TobiasJaeggi/fpga-mocap/visionAddOn/pcb/3DModels/RT2012-32.768-9-20-EXT-TR.stp

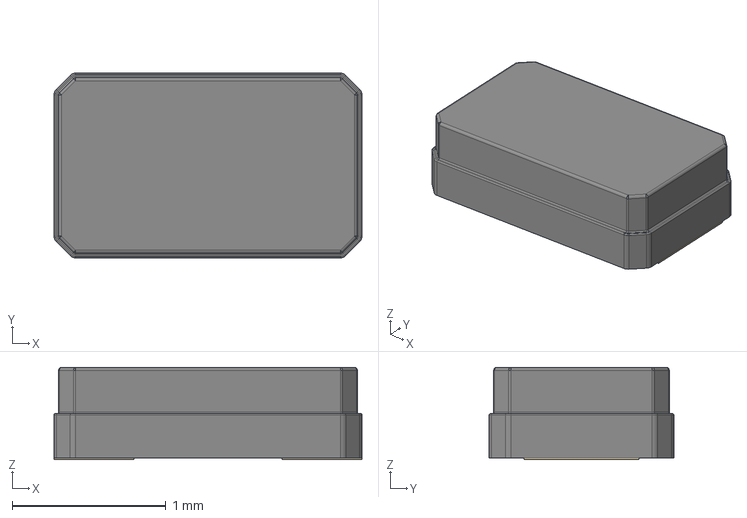
[picture p15: CAD file, 2025-07-20]
visionAddOn/pcb/3DModels/RT2012-32.768-9-20-EXT-TR.stp
2.00 x 1.20 x 0.6 mm
