TobiasJaeggi/fpga-mocap/visionAddOn/pcb/3DModels/Amass_XT30UPB-F.step

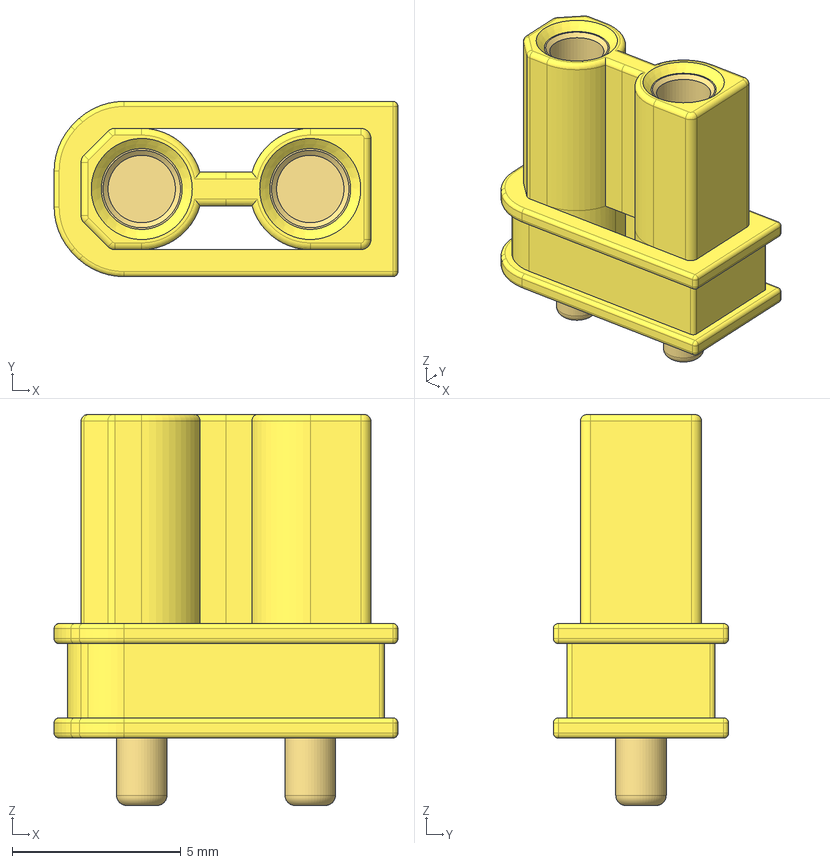
[picture p16: CAD file, 2025-07-20]
visionAddOn/pcb/3DModels/Amass_XT30UPB-F.step
10.2 x 5.20 x 11.6 mm
