TobiasJaeggi/fpga-mocap/visionAddOn/pcb/3DModels/USB2513B-AEZC-TR.STEP

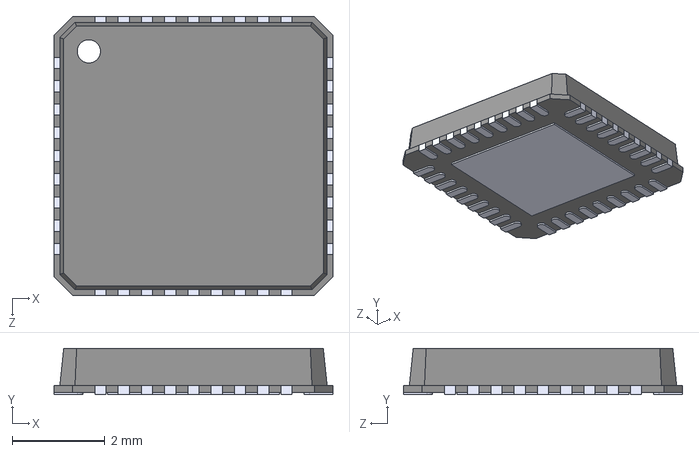
[picture p17: CAD file, 2025-07-20]
visionAddOn/pcb/3DModels/USB2513B-AEZC-TR.STEP
6.00 x 1.00 x 6.00 mm
