TobiasJaeggi/fpga-mocap/visionAddOn/pcb/3DModels/ARJP11A-MASA-B-A-EMU2--3DModel-STEP-1.STEP

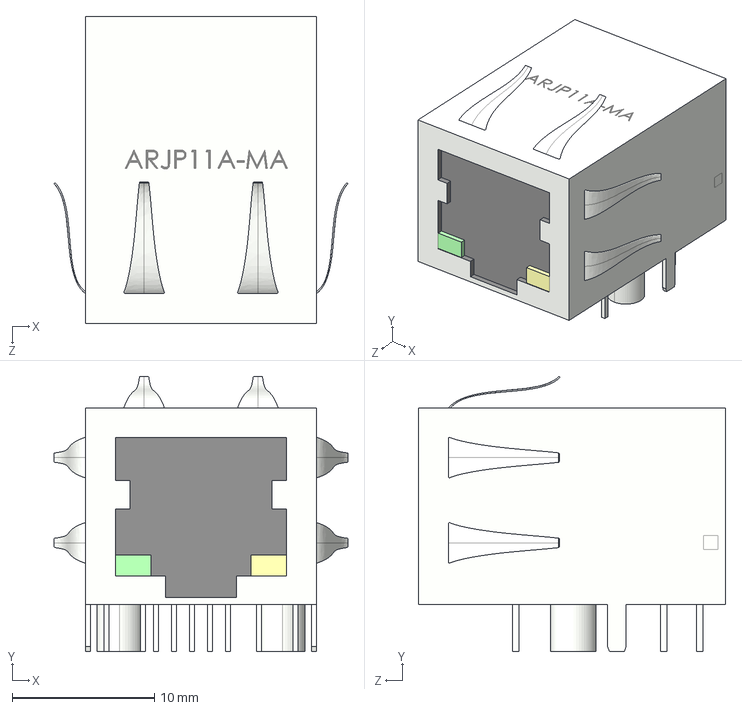
[picture p18: CAD file, 2025-07-20]
visionAddOn/pcb/3DModels/ARJP11A-MASA-B-A-EMU2--3DModel-STEP-1.STEP
20.7 x 19.3 x 21.6 mm
