TobiasJaeggi/fpga-mocap/visionAddOn/pcb/3DModels/LAN8742A-CZ-TR--3DModel-STEP-510211.STEP

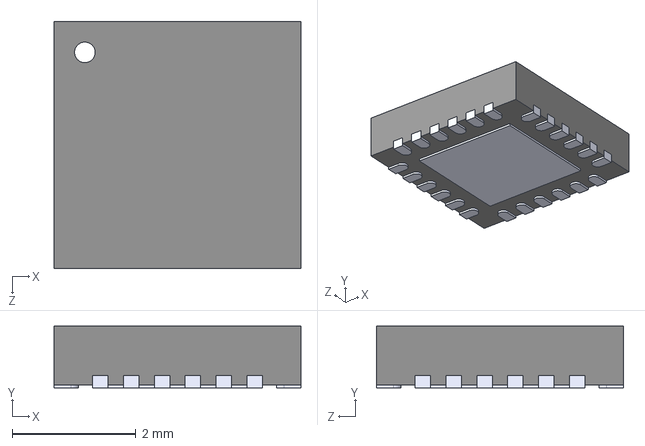
[picture p19: CAD file, 2025-07-20]
visionAddOn/pcb/3DModels/LAN8742A-CZ-TR--3DModel-STEP-510211.STEP
4.00 x 1.00 x 4.00 mm
