TobiasJaeggi/fpga-mocap/visionAddOn/pcb/3DModels/NTS0104BQ_115.step

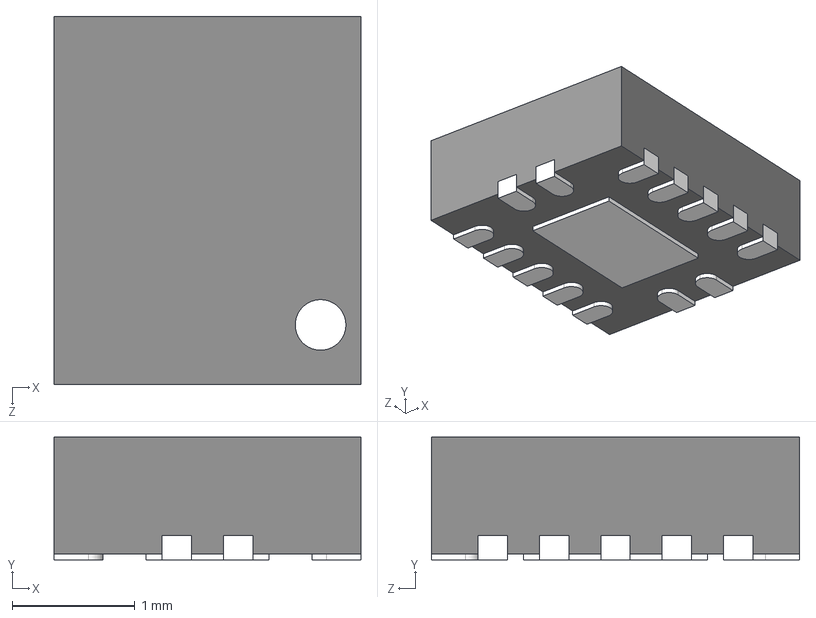
[picture p20: CAD file, 2025-07-20]
visionAddOn/pcb/3DModels/NTS0104BQ_115.step
2.50 x 1.00 x 3.00 mm
