TobiasJaeggi/fpga-mocap/visionAddOn/pcb/3DModels/MYBSP0055AABFT--3DModel-STEP-387902.STEP

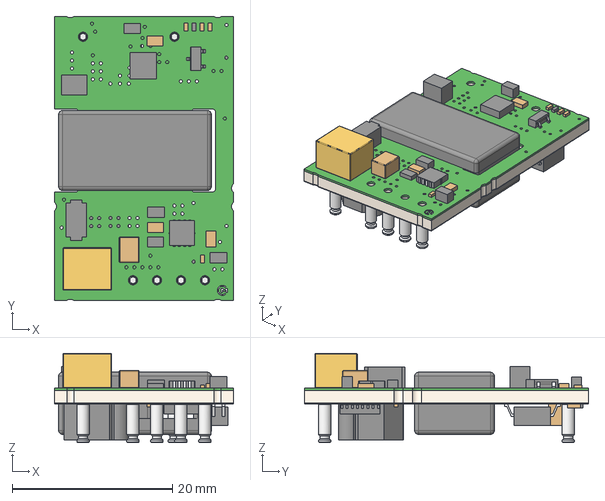
[picture p21: CAD file, 2025-07-20]
visionAddOn/pcb/3DModels/MYBSP0055AABFT--3DModel-STEP-387902.STEP
22.4 x 35.5 x 11.1 mm
