TobiasJaeggi/fpga-mocap/visionAddOn/pcb/3DModels/QTE-020-01-X-D-A.step

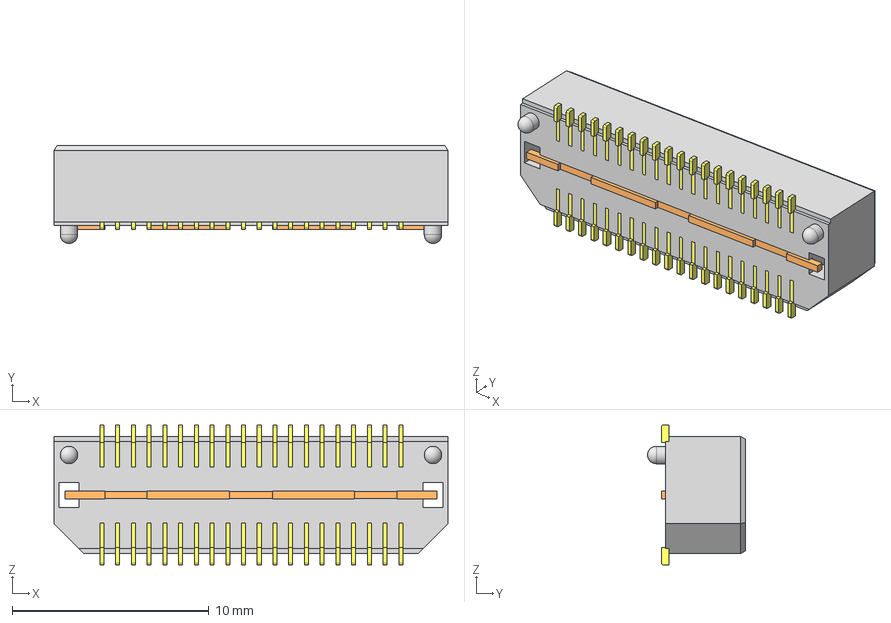
[picture p22: CAD file, 2025-07-20]
visionAddOn/pcb/3DModels/QTE-020-01-X-D-A.step
20.0 x 4.98 x 7.11 mm
QTE-T-1G1-01_imp
PT-1S39-01(020-01-D)
QTE-020-01-D-At
