TobiasJaeggi/fpga-mocap/visionAddOn/pcb/3DModels/LQM2HPN2R2MJ0L.STEP

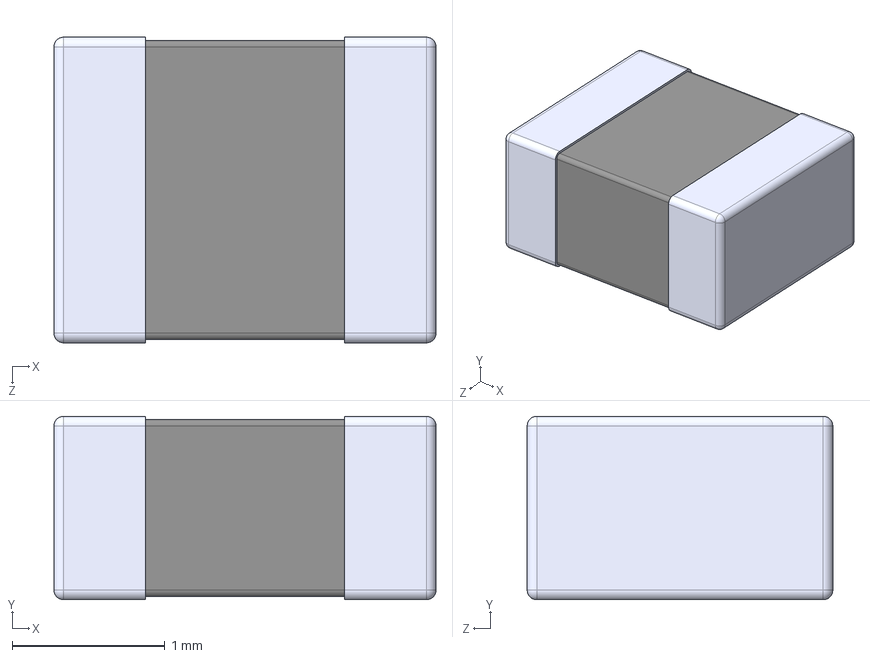
[picture p23: CAD file, 2025-07-20]
visionAddOn/pcb/3DModels/LQM2HPN2R2MJ0L.STEP
2.50 x 1.20 x 2.00 mm
