TobiasJaeggi/fpga-mocap/visionAddOn/firmware/Core/Src/main.cpp

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
/* Includes ------------------------------------------------------------------*/
#include "main.h"
#include "cmsis_os.h"
#include "dcmi.h"
#include "dma.h"
#include "i2c.h"
#include "lwip.h"
#include "spi.h"
#include "usart.h"
#include "usb_otg.h"
#include "gpio.h"
#include "fmc.h"

/* USER CODE BEGIN Includes */

#include <stdio.h>
/* USER CODE END Includes */

/* USER CODE BEGIN PD */
#define TEST_EXTERNAL_SDRAM
#define LWIP_DEBUG 1
#undef SOCKETS_DEBUG
#define SOCKETS_DEBUG LWIP_DBG_ON
#undef MEM_DEBUG
#define MEM_DEBUG LWIP_DBG_ON
#undef MEMP_DEBUG
#define MEMP_DEBUG LWIP_DBG_ON
/* USER CODE END PD */


void SystemClock_Config(void);
void MX_FREERTOS_Init(void);
/* USER CODE BEGIN 0 */
}
#include "AppBuilder.h"
#include "utils/swo.h"
#include "utils/Log.h"
#include "utils/constants.h"
#include "as4c16m16msa/sdram.h"
/* USER CODE END 0 */

/**
  * @brief  The application entry point.
  * @retval int
  */
int main(void)
{

  /* MCU Configuration--------------------------------------------------------*/

  /* Reset of all peripherals, Initializes the Flash interface and the Systick. */
  HAL_Init();

  /* Configure the system clock */
  SystemClock_Config();

  /* Initialize all configured peripherals */
  MX_GPIO_Init();
  MX_DMA_Init();
  MX_DCMI_Init();
  MX_FMC_Init();
  MX_USART1_UART_Init();
  MX_USART2_UART_Init();
  MX_I2C1_Init();
  MX_SPI1_Init();
  MX_I2C4_Init();
  MX_SPI5_Init();
  MX_UART5_Init();
  MX_USB_OTG_HS_PCD_Init();
  /* USER CODE BEGIN 2 */
  Log::registerTickKeeper([](void) -> uint32_t {return osKernelGetTickCount();});
  Log::setTickrate(TICKS_PER_MILLISECOND);
  Log::level(Log::Level::LOG_INFO);
  Log::info("[main] visionAddOn, commit %s", GIT_COMMIT_HASH);

  initSdram(&hsdram1);
#ifdef TEST_EXTERNAL_SDRAM
  Log::info("[main] testing sdram");
  uint32_t* externalSdramBase = (uint32_t*) EXTERNAL_SDRAM_BASE_ADDRESS;
  for(uint32_t offset = 0; offset < EXTERNAL_SDRAM_SIZE_WORDS; offset++) {
    if((EXTERNAL_SDRAM_BASE_ADDRESS + offset) > EXTERNAL_SDRAM_END_ADDRESS) {
      Log::error("[main] @ offset %#x: EXTERNAL_SDRAM_BASE_ADDRESS + offset = %#x, which is greater than EXTERNAL_SDRAM_END_ADDRESS (%#x)", offset, EXTERNAL_SDRAM_BASE_ADDRESS + offset, EXTERNAL_SDRAM_END_ADDRESS);
      Error_Handler();
    }
    externalSdramBase[offset] = offset;
    uint32_t offsetReadBack = externalSdramBase[offset];
    if(offset != offsetReadBack) {
      Log::error("[main] offset: %#x, offsetReadBack: %#x", offset, offsetReadBack);
      Error_Handler();
    }
  }
  Log::info("[main] sdram ok");
#endif // TEST_EXTERNAL_SDRAM

  /* USER CODE END 2 */

  /* Init scheduler */
  osKernelInitialize();

  /* Call init function for freertos objects (in cmsis_os2.c) */
  MX_FREERTOS_Init();

  /* Start scheduler */
  osKernelStart();

  /* We should never get here as control is now taken by the scheduler */

  /* Infinite loop */
  /* USER CODE BEGIN WHILE */

  
  while (1)
  {
    /* USER CODE END WHILE */

    /* USER CODE BEGIN 3 */
  } // extern C
// ignore the shitty RCC_OscInitStruct and RCC_ClkInitStruct initialization
#pragma GCC diagnostic push
#pragma GCC diagnostic ignored "-Wmissing-field-initializers"
  /* USER CODE END 3 */
}

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
/* USER CODE BEGIN 4 */
#pragma GCC diagnostic pop // "-Wmissing-field-initializers"
/* USER CODE END 4 */

/**
  * @brief  Period elapsed callback in non blocking mode
  * @note   This function is called  when TIM1 interrupt took place, inside
  * HAL_TIM_IRQHandler(). It makes a direct call to HAL_IncTick() to increment
  * a global variable "uwTick" used as application time base.
  * @param  htim : TIM handle
  * @retval None
  */
void HAL_TIM_PeriodElapsedCallback(TIM_HandleTypeDef *htim)
{
  if (htim->Instance == TIM1) {
    HAL_IncTick();
  }
}

/**
  * @brief  This function is executed in case of error occurrence.
  * @retval None
  */
void Error_Handler(void)
{
  /* USER CODE BEGIN Error_Handler_Debug */
  /* User can add his own implementation to report the HAL error return state */
  __disable_irq();
  log_error("[Error_Handler]");
  abort();
  /* USER CODE END Error_Handler_Debug */
}

#ifdef  USE_FULL_ASSERT
/**
  * @brief  Reports the name of the source file and the source line number
  *         where the assert_param error has occurred.
  * @param  file: pointer to the source file name
  * @param  line: assert_param error line source number
  * @retval None
  */
void assert_failed(uint8_t *file, uint32_t line)
{
  /* USER CODE BEGIN 6 */
  /* User can add his own implementation to report the file name and line number,
     ex: printf("Wrong parameters value: file %s on line %d\r\n", file, line) */
  /* USER CODE END 6 */
}
#endif /* USE_FULL_ASSERT */
