TobiasJaeggi/fpga-mocap/visionAddOn/pcb/STM32F767ZIx/STM32F767ZIx.ioc

Mcu.UserName=STM32F767ZITx
PA0/WKUP.GPIO_Label=STM_DBG_10
PA0/WKUP.Signal=GPIO_Input
PA1.Signal=ETH_REF_CLK
PA10.Signal=USART1_RX
PA11.Signal=USART1_CTS
PA12.Signal=USART1_RTS
PA13.GPIO_Label=TMS
PA13.Signal=SYS_JTMS-SWDIO
PA14.GPIO_Label=TCK
PA14.Signal=SYS_JTCK-SWCLK
PA15.Signal=SYS_JTDI
PA2.Signal=ETH_MDIO
PA3.Signal=USART2_RX
PA4.Signal=DCMI_HSYNC
PA5.Signal=SPI1_SCK
PA6.Signal=DCMI_PIXCLK
PA7.Signal=ETH_CRS_DV
PA8.GPIO_Label=STM_DBG_11
PA8.Signal=GPIO_Input
PA9.Signal=USART1_TX
PB0.GPIO_Label=STM_DBG_15
PB0.Signal=GPIO_Input
PB1.GPIO_Label=STM_DBG_16
PB1.Signal=GPIO_Input
PB10.GPIO_Label=STM_DBG_21
PB10.Signal=GPIO_Input
PB11.Signal=ETH_TX_EN
PB12.Signal=ETH_TXD0
PB13.Signal=ETH_TXD1
PB14.Signal=USB_OTG_HS_DM
PB15.Signal=USB_OTG_HS_DP
PB2.GPIO_Label=STM_DBG_17
PB2.Signal=GPIO_Input
PB3.GPIO_Label=SWO
PB3.Signal=SYS_JTDO-SWO
PB4.Signal=SPI1_MISO
PB5.GPIO_Label=STM_DBG_18
PB5.Signal=GPIO_Input
PB6.Signal=I2C1_SCL
PB7.Signal=I2C1_SDA
PB8.Signal=UART5_RX
PB9.Signal=UART5_TX
PC0.Signal=FMC_SDNWE
PC1.Signal=ETH_MDC
PC10.GPIO_Label=STM_DBG_23
PC10.Signal=GPIO_Input
PC11.GPIO_Label=STM_DBG_24
PC11.Signal=GPIO_Input
PC12.GPIO_Label=STM_DBG_20
PC12.Signal=GPIO_Input
PC13.GPIO_Label=BUTTON1
PC13.Signal=GPIO_Input
PC14/OSC32_IN.Signal=RCC_OSC32_IN
PC15/OSC32_OUT.Signal=RCC_OSC32_OUT
PC2.Signal=FMC_SDNE0
PC3.Signal=FMC_SDCKE0
PC4.Signal=ETH_RXD0
PC5.Signal=ETH_RXD1
PC6.Signal=DCMI_D0
PC7.Signal=DCMI_D1
PC8.Signal=DCMI_D2
PC9.Signal=DCMI_D3
PD0.Signal=FMC_D2_DA2
PD1.Signal=FMC_D3_DA3
PD10.Signal=FMC_D15_DA15
PD11.GPIO_Label=WATCHDOG
PD11.Signal=GPIO_Output
PD12.Signal=I2C4_SCL
PD13.Signal=I2C4_SDA
PD14.Signal=FMC_D0_DA0
PD15.Signal=FMC_D1_DA1
PD2.GPIO_Label=STM_DBG_19
PD2.Signal=GPIO_Input
PD3.Signal=DCMI_D5
PD4.GPIO_Label=STM_DBG_8
PD4.Signal=GPIO_Input
PD5.Signal=USART2_TX
PD6.GPIO_Label=STM_DGB_25
PD6.Signal=GPIO_Input
PD7.Signal=SPI1_MOSI
PD8.Signal=FMC_D13_DA13
PD9.Signal=FMC_D14_DA14
PE0.Signal=FMC_NBL0
PE1.Signal=FMC_NBL1
PE10.Signal=FMC_D7_DA7
PE11.Signal=FMC_D8_DA8
PE12.Signal=FMC_D9_DA9
PE13.Signal=FMC_D10_DA10
PE14.Signal=FMC_D11_DA11
PE15.Signal=FMC_D12_DA12
PE2.GPIO_Label=LED_RED
PE2.Signal=GPIO_Output
PE3.GPIO_Label=LED_GREEN
PE3.Signal=GPIO_Output
PE4.Signal=DCMI_D4
PE5.Signal=DCMI_D6
PE6.Signal=DCMI_D7
PE7.Signal=FMC_D4_DA4
PE8.Signal=FMC_D5_DA5
PE9.Signal=FMC_D6_DA6
PF0.Signal=FMC_A0
PF1.Signal=FMC_A1
PF10.GPIO_Label=STM_DBG_9
PF10.Signal=GPIO_Input
PF11.Signal=FMC_SDNRAS
PF12.Signal=FMC_A6
PF13.Signal=FMC_A7
PF14.Signal=FMC_A8
PF15.Signal=FMC_A9
PF2.Signal=FMC_A2
PF3.Signal=FMC_A3
PF4.Signal=FMC_A4
PF5.Signal=FMC_A5
PF6.GPIO_Label=POE_TYPE
PF6.Signal=GPIO_Input
PF7.Signal=SPI5_SCK
PF8.Signal=SPI5_MISO
PF9.Signal=SPI5_MOSI
PG0.Signal=FMC_A10
PG1.Signal=FMC_A11
PG10.GPIO_Label=STM_DBG_3
PG10.Signal=GPIO_Input
PG11.GPIO_Label=STM_DBG_4
PG11.Signal=GPIO_Input
PG12.GPIO_Label=STM_DBG_5
PG12.Signal=GPIO_Input
PG13.GPIO_Label=STM_DBG_6
PG13.Signal=GPIO_Input
PG14.GPIO_Label=STM_DBG_7
PG14.Signal=GPIO_Input
PG15.Signal=FMC_SDNCAS
PG2.Signal=FMC_A12
PG3.GPIO_Label=STM_DBG_0
PG3.Signal=GPIO_Input
PG4.Signal=FMC_A14_BA0
PG5.Signal=FMC_A15_BA1
PG6.GPIO_Label=STM_DBG_1
PG6.Signal=GPIO_Input
PG7.GPIO_Label=STM_DBG_2
PG7.Signal=GPIO_Input
PG8.Signal=FMC_SDCLK
PG9.Signal=DCMI_VSYNC
PH0/OSC_IN.Signal=RCC_OSC_IN
PH1/OSC_OUT.Signal=RCC_OSC_OUT
