TobiasJaeggi/fpga-mocap/gecko5/hdl/modules/counters/verilog/intCounter.v

module intCounter #(parameter MAX = 20) (
  input wire clock,
  input wire reset,
  input wire clear,
  input wire load,
  input wire enable,
  input wire [$clog2(MAX)-1:0] din,
  output wire max_pulse,
  output wire [$clog2(MAX)-1:0] dout
);

reg[$clog2(MAX)-1:0] s_stateNext, s_stateReg;

//TODO: async reset
always @(posedge clock)
begin
  s_stateReg <= ((reset == 1'b1) || (s_stateNext == $clog2(MAX)'(MAX))) ? 0 : s_stateNext;
end

// NSL
assign s_stateNext =  clear ? 0 :
                      load ? din : 
                      enable ? s_stateReg + 1 : 
                      s_stateReg;  

// OL
assign max_pulse = (s_stateReg == $clog2(MAX)'(MAX-1)) ? 1 : 0;
assign dout = s_stateReg;

endmodule
