TobiasJaeggi/fpga-mocap/gecko5/hdl/programs/blobDetector/include/waitForTransfer.h

#ifndef WAITFORTRANSFER_H_INCLUDED
#define WAITFORTRANSFER_H_INCLUDED

#include <stdint.h>

#ifdef __cplusplus
extern "C" {
#endif

uint32_t waitForTransferBlocking();

#ifdef __cplusplus
}
#endif

#endif /* WAITFORTRANSFER_H_INCLUDED */
