TobiasJaeggi/fpga-mocap/gecko5/hdl/programs/blobDetector/support/include/ov7670.h

#ifndef __OV7670_H__
#define __OV7670_H__
#include <stdint.h>
#include <stdbool.h>

  /*
   * this code is a copy/modification of the code presented:
   * https://github.com/ComputerNerd/ov7670-no-ram-arduino-uno
   */

typedef enum resolution_t {VGA,QVGA,QQVGA} resolution;
typedef enum framerate_t {_15,_30} framerate;
typedef struct camParam_t {
  uint32_t nrOfPixelsPerLine;
  uint32_t nrOfLinesPerImage;
  uint32_t pixelClockInkHz;
  uint32_t framesPerSecond;
} camParameters;

int readOv7670Register( int reg );
void writeOv7670Register(int reg , int value);
camParameters initOv7670(resolution res, framerate fps);
void takeSingleImageBlocking(uint32_t framebuffer);
void takeSingleImageNonBlocking(uint32_t framebuffer);
void waitForNextImage();
void enableContinues(uint32_t framebuffer);
void disableContinues();
void autoExposure(bool enable);
void setExposure(uint8_t value);
void autoWhitebalance(bool enable);
void setWhiteBalanceBlue(uint8_t value);
void setWhiteBalanceRed(uint8_t value);
void autoGain(bool enable);
void setGain(uint8_t value);
#endif
