TobiasJaeggi/fpga-mocap/visionAddOn/firmware/App/camera/CameraTypes.h

#ifndef VISIONADDON_APP_CAMERA_TYPES_H
#define VISIONADDON_APP_CAMERA_TYPES_H

#include <cstdint>

enum Fps : uint8_t
{
    _13 = 0,
    _72 = 1,
    UNDEFINED = 0xff,
};

#endif // VISIONADDON_APP_CAMERA_TYPES_H
